NotoFederico/VoltAmmeter/Firmware/Bibliotecas/Display 4x20/lcd.h

void init_lcd(void);
void cls_lcd(void);
void posic_lcd(char adress);
void lcd_wr_data4bits (char datos);
void wrchar(unsigned char dato);
void print (char cadena[]);
void print1 (char cadena[]);
void print2 (char cadena[]);
void print3 (char cadena[]);
void print4 (char cadena[]);
